shop2007/Amperometro_con_soglia/dc-dc-24-5.jpg

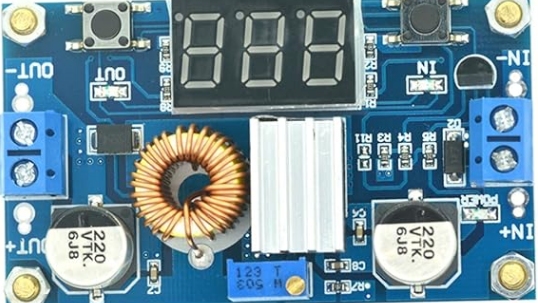
dc-dc-24-5.jpg
