shop2007/Amperometro_con_soglia/doc/pic/Cablaggio.jpg

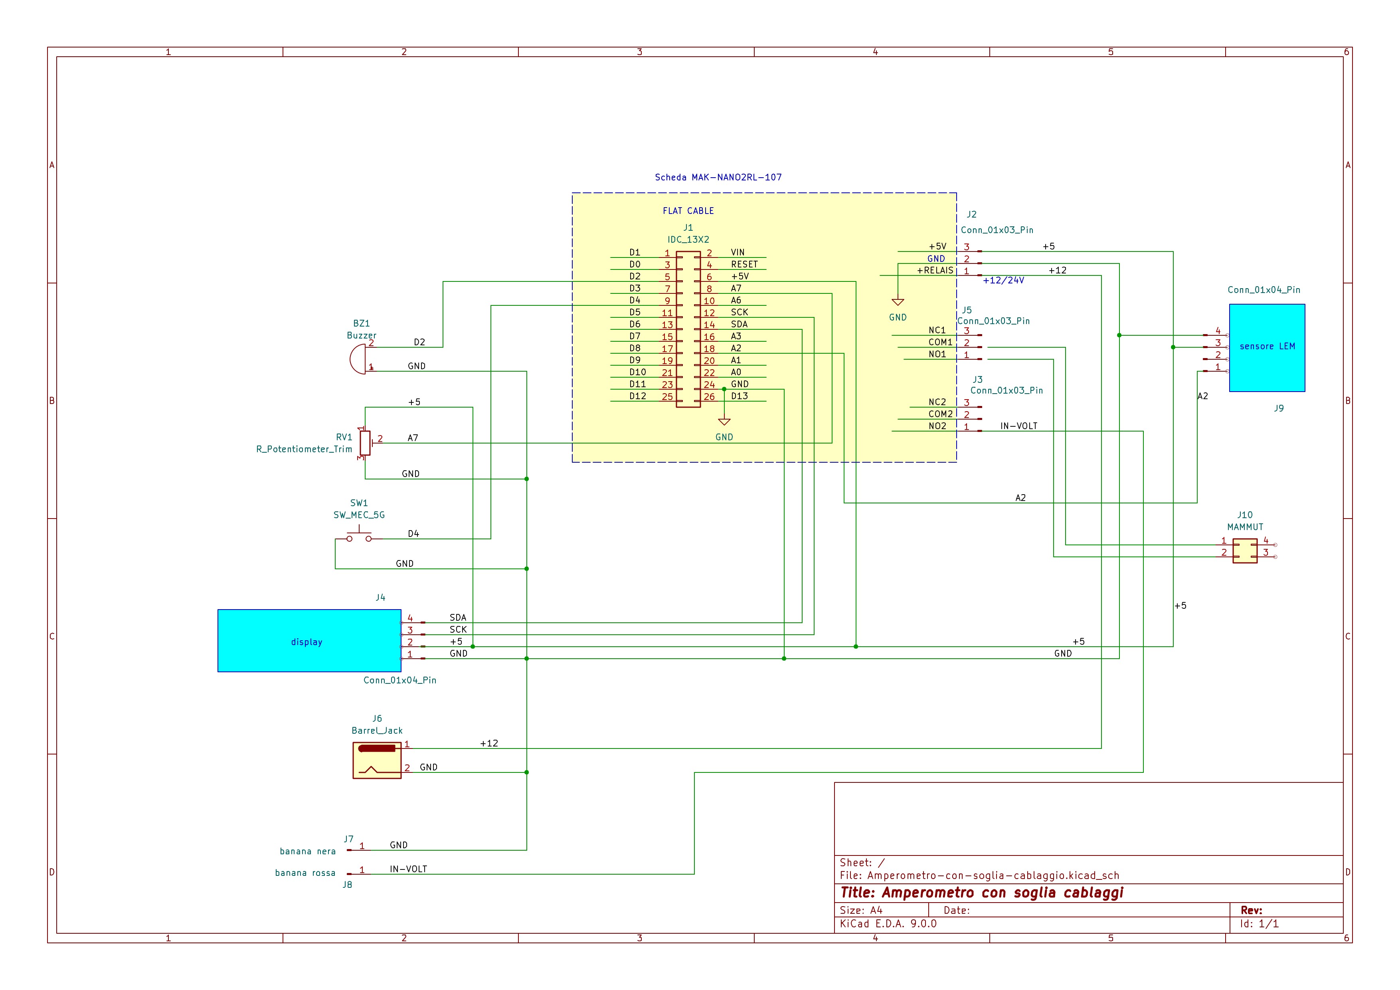
doc/pic/Cablaggio.jpg
