shop2007/Amperometro_con_soglia/doc/pic/Immagine 1.jpg

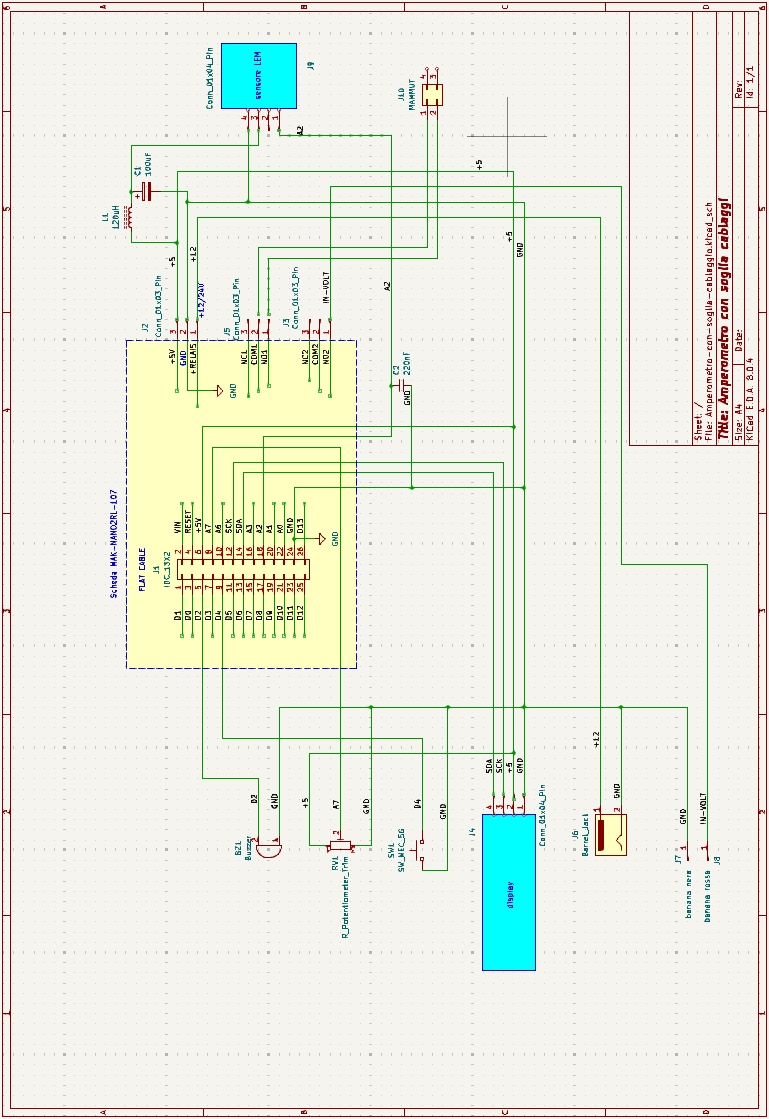
doc/pic/Immagine 1.jpg
