shop2007/Amperometro_con_soglia/doc/pic/Stampa schema - Amperomentro schema vers. SMS.jpg

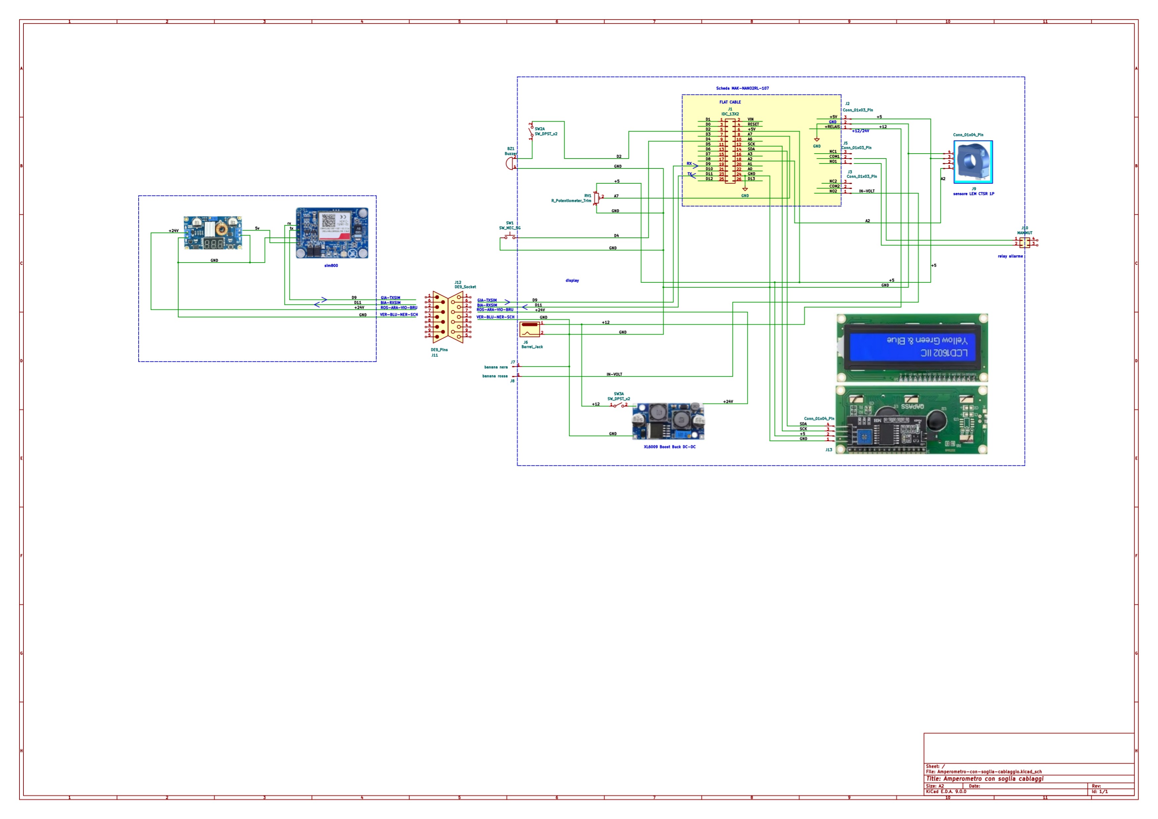
doc/pic/Stampa schema - Amperomentro schema vers. SMS.jpg
