shop2007/Amperometro_con_soglia/kicad/img/LCD1602 I2CAdattatore IIC.png

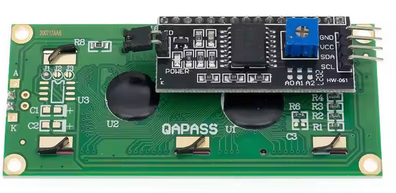
kicad/img/LCD1602 I2CAdattatore IIC.png
