shop2007/Amperometro_con_soglia/kicad/img/lem.jpg

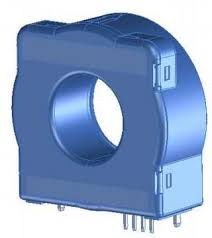
kicad/img/lem.jpg
