shop2007/Amperometro_con_soglia/proto2.jpg

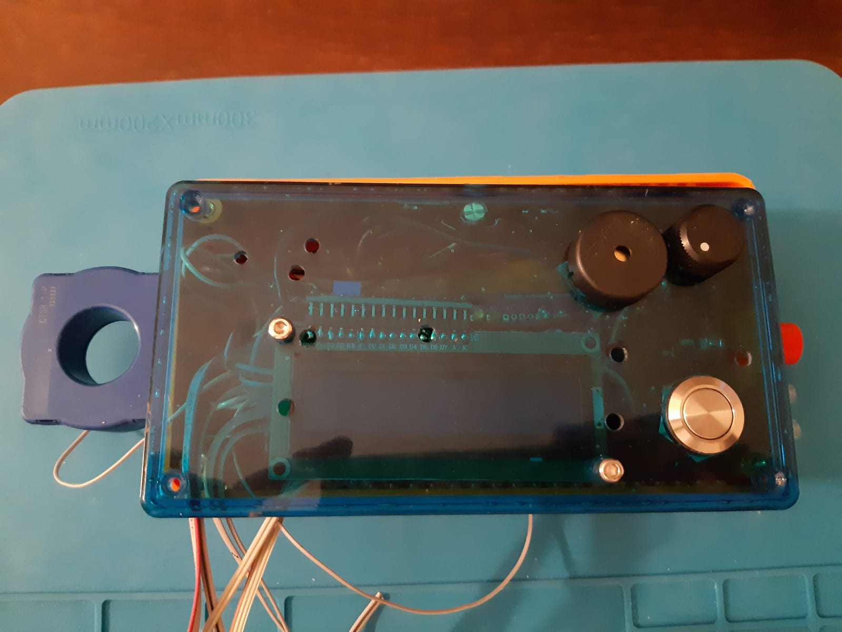
proto2.jpg
