shop2007/Amperometro_con_soglia/proto3.jpg

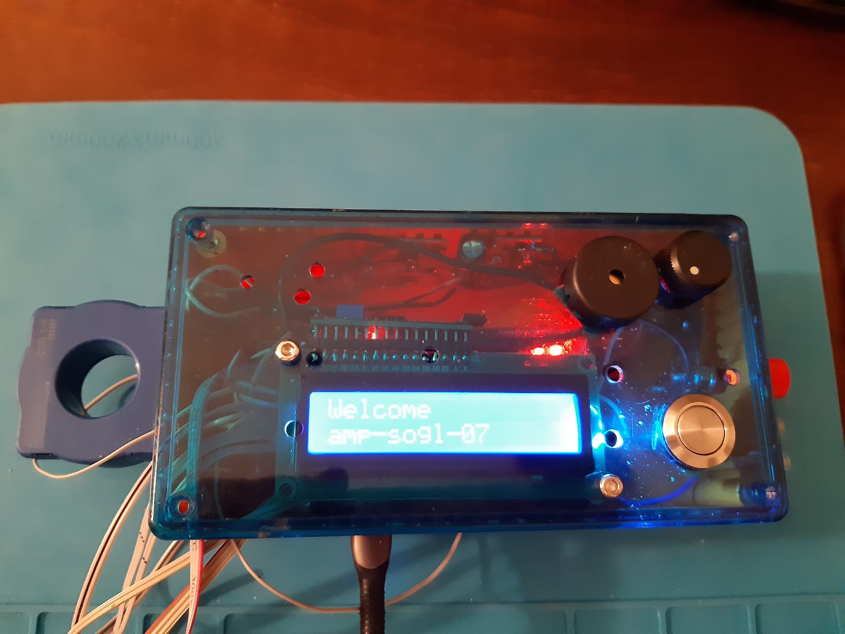
proto3.jpg
