shop2007/Amperometro_con_soglia/proto4.jpg

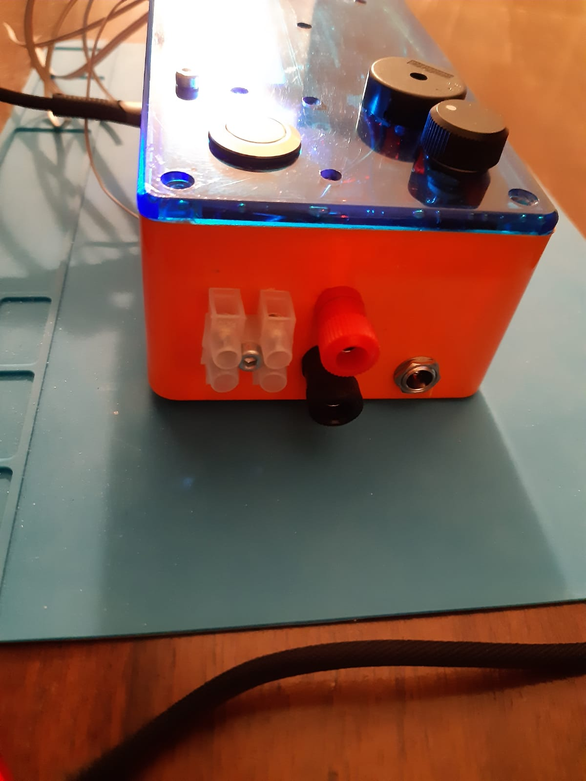
proto4.jpg
