shop2007/Amperometro_con_soglia/proto.jpg

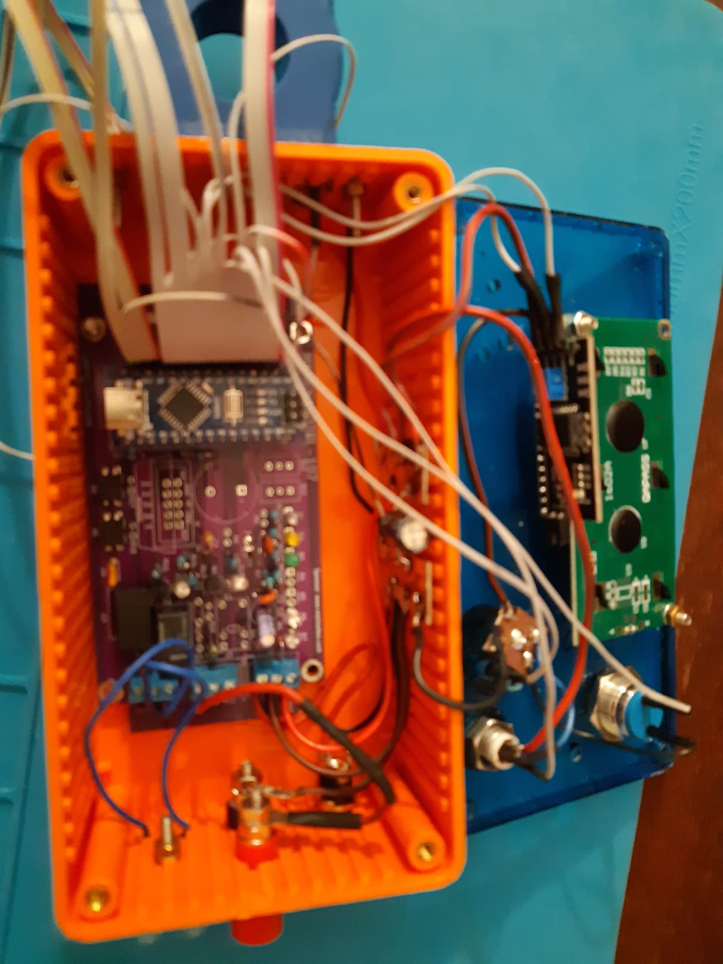
proto.jpg
