shop2007/Amperometro_con_soglia/sim800/Acquisizioni Oscilloscopio/140 connesso verde I_SIM 0.5a-div viola V_SIM 2v-div vswin18v.BMP

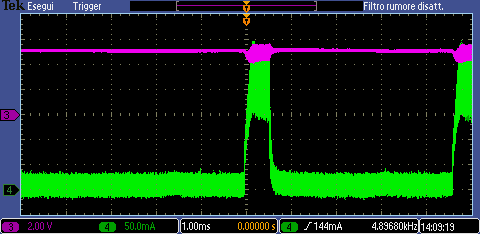
sim800/Acquisizioni Oscilloscopio/140 connesso verde I_SIM 0.5a-div viola V_SIM 2v-div vswin18v.BMP
