shop2007/Amperometro_con_soglia/sim800/Acquisizioni Oscilloscopio/149 fallimento verde I_SIM 1a-div viola V_SIM 2v-div vswin12v.BMP

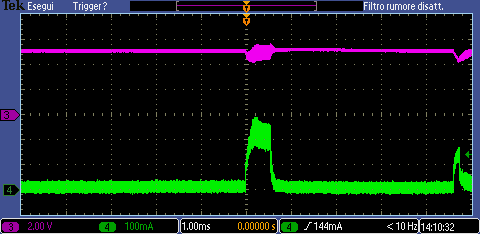
sim800/Acquisizioni Oscilloscopio/149 fallimento verde I_SIM 1a-div viola V_SIM 2v-div vswin12v.BMP
