shop2007/Amperometro_con_soglia/sim800/Acquisizioni Oscilloscopio/TEK00141.BMP

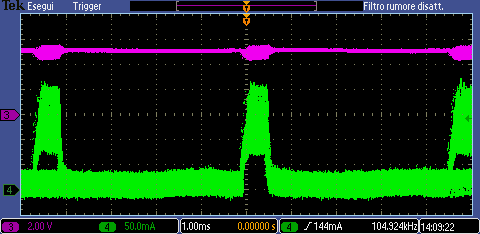
sim800/Acquisizioni Oscilloscopio/TEK00141.BMP
