shop2007/Amperometro_con_soglia/sim800/Acquisizioni Oscilloscopio/TEK00143.BMP

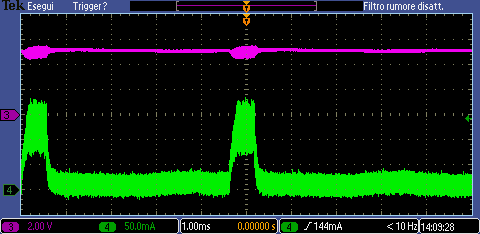
sim800/Acquisizioni Oscilloscopio/TEK00143.BMP
