shop2007/Amperometro_con_soglia/sim800/SCHEMA .png

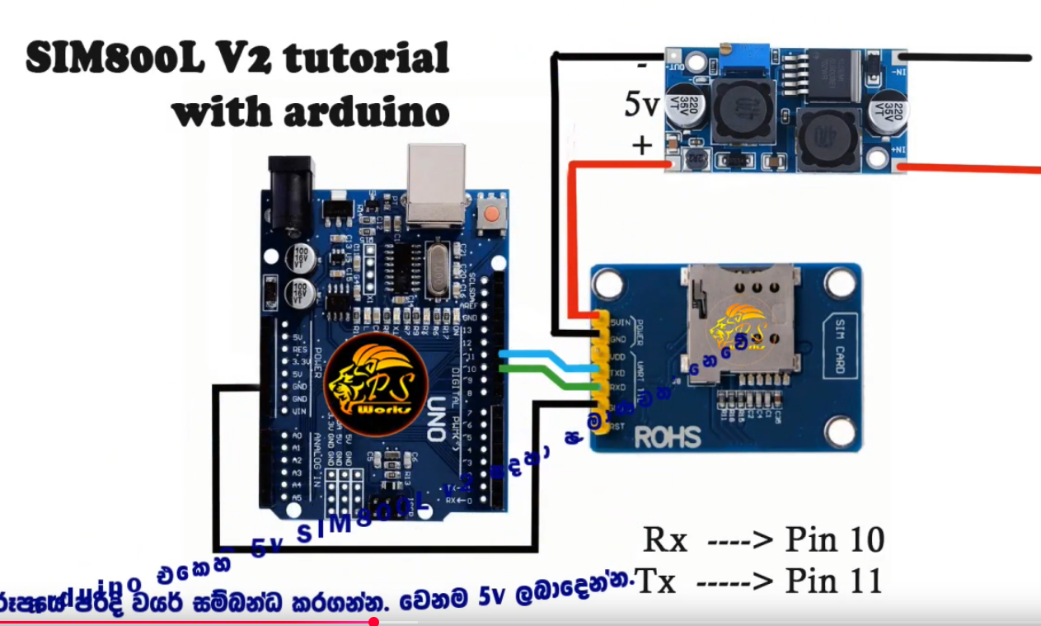
sim800/SCHEMA .png
