shop2007/Amperometro_con_soglia/sim800/YOUTUBE/SIM800L.jpg

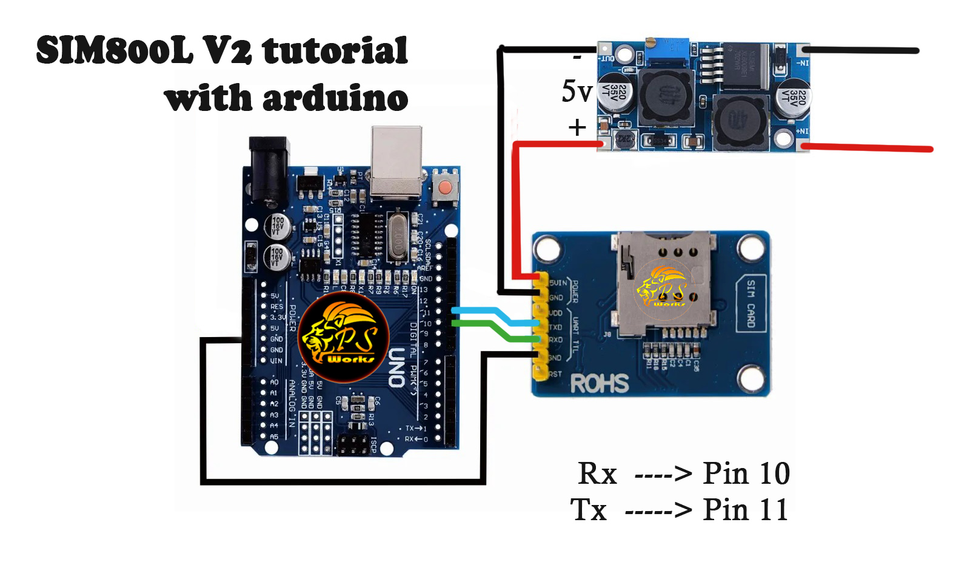
sim800/YOUTUBE/SIM800L.jpg
