shop2007/Amperometro_con_soglia/sim800/YOUTUBE/thumbl.jpg

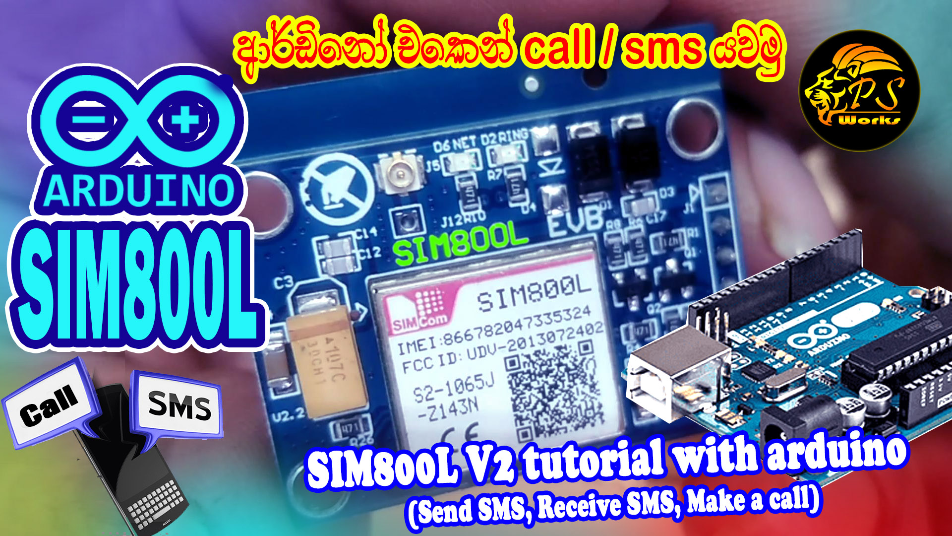
sim800/YOUTUBE/thumbl.jpg
