shop2007/Amperometro_con_soglia/doc/Amperomentro schema vers. SMS.pdf

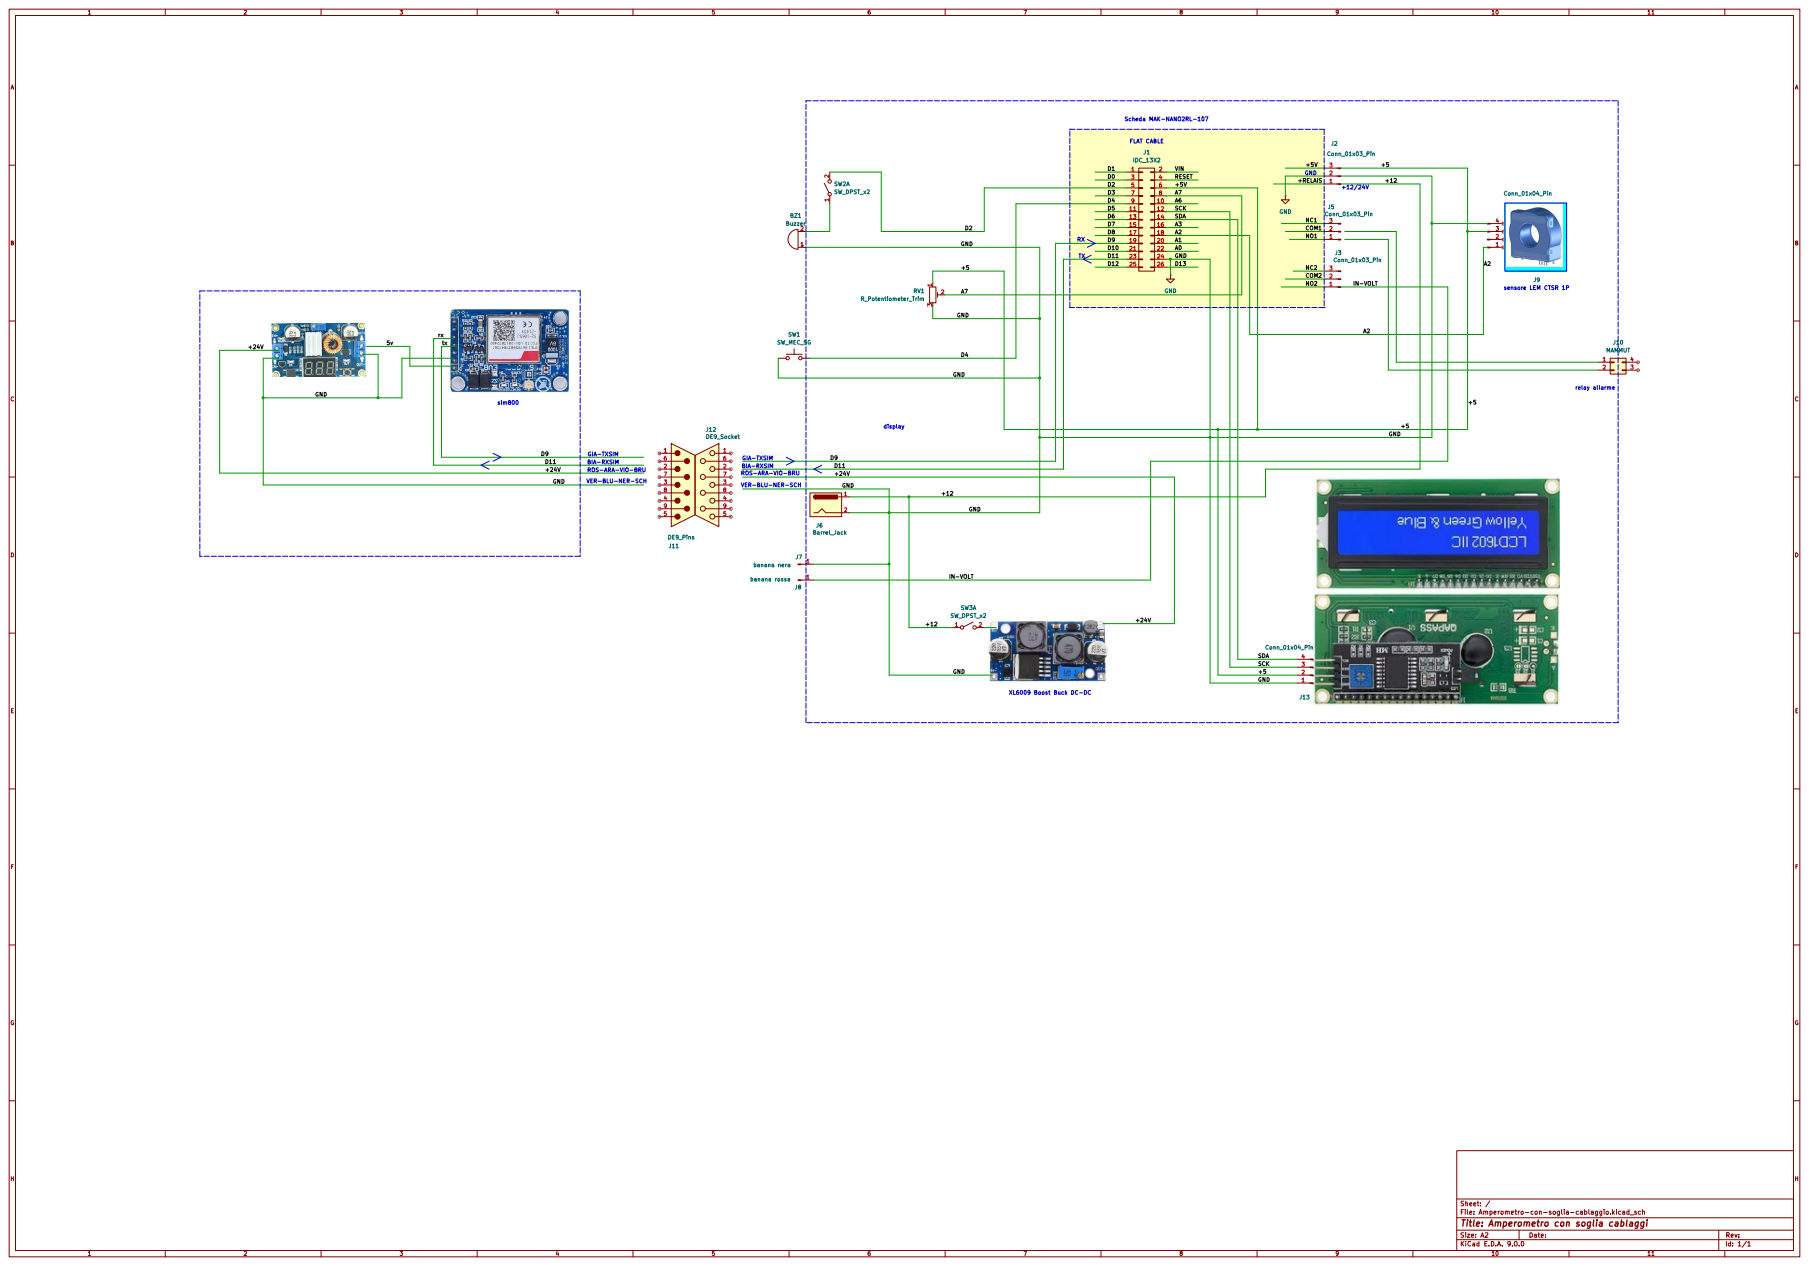
[picture p66: page 1]
