shop2007/Amperometro_con_soglia/kicad/Amperometro-con-soglia-cablaggio.kicad_sch

## KiCad design kicad/Amperometro-con-soglia-cablaggio.kicad_sch (2025-05-17)

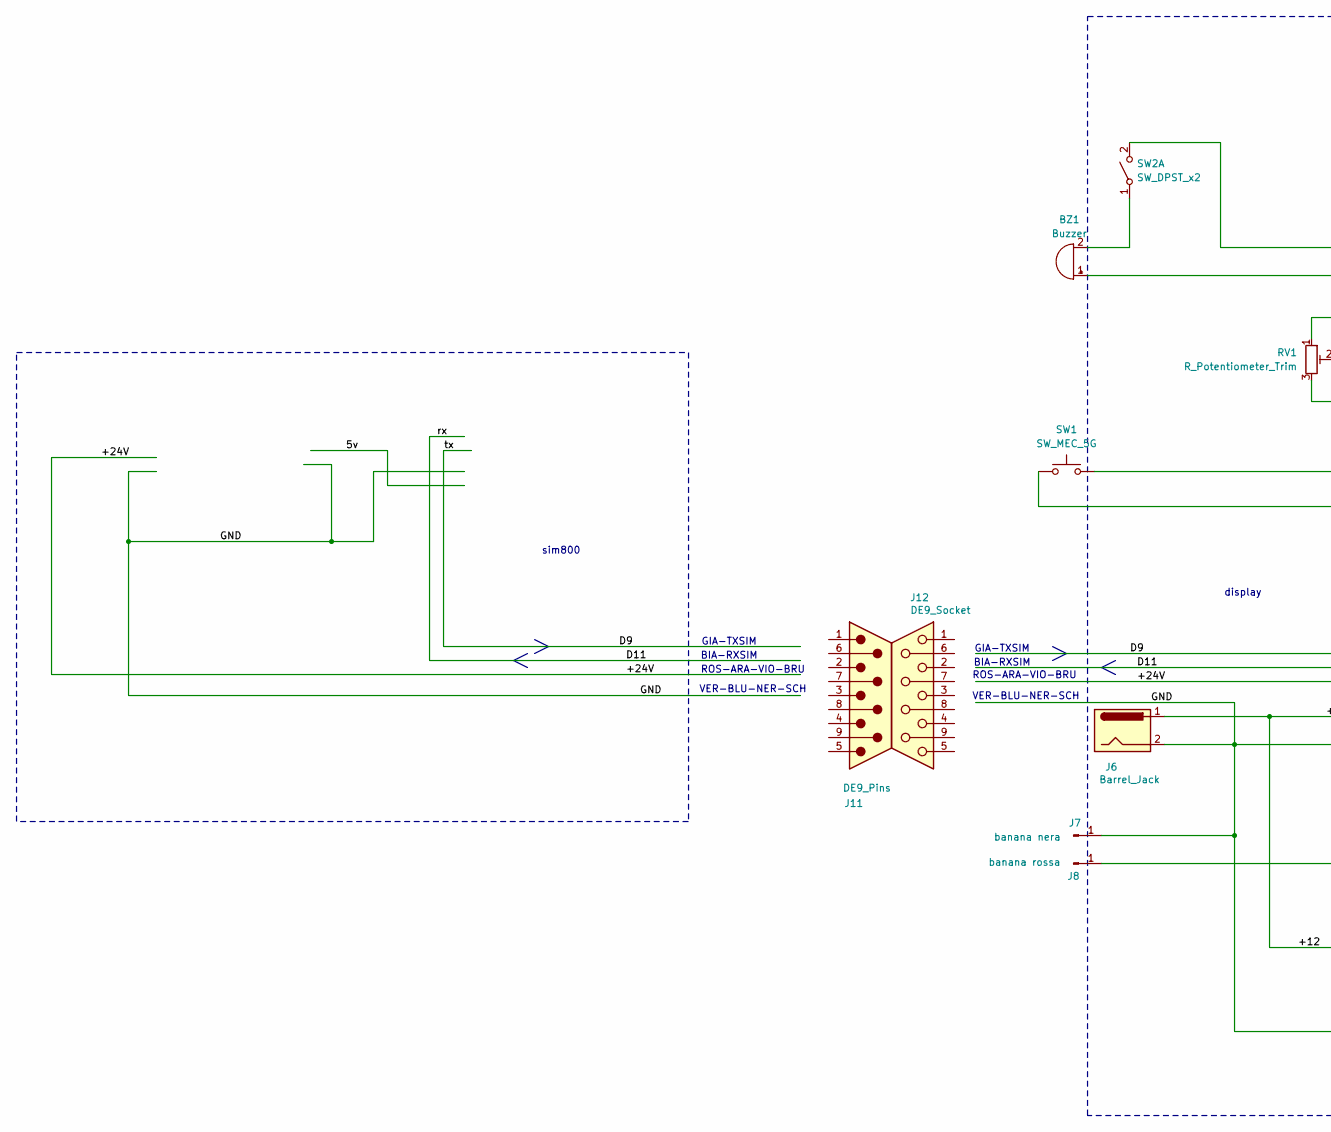
[picture p67: schematic Amperometro-con-soglia-cablaggio.kicad_sch, part in row 1, column 1]

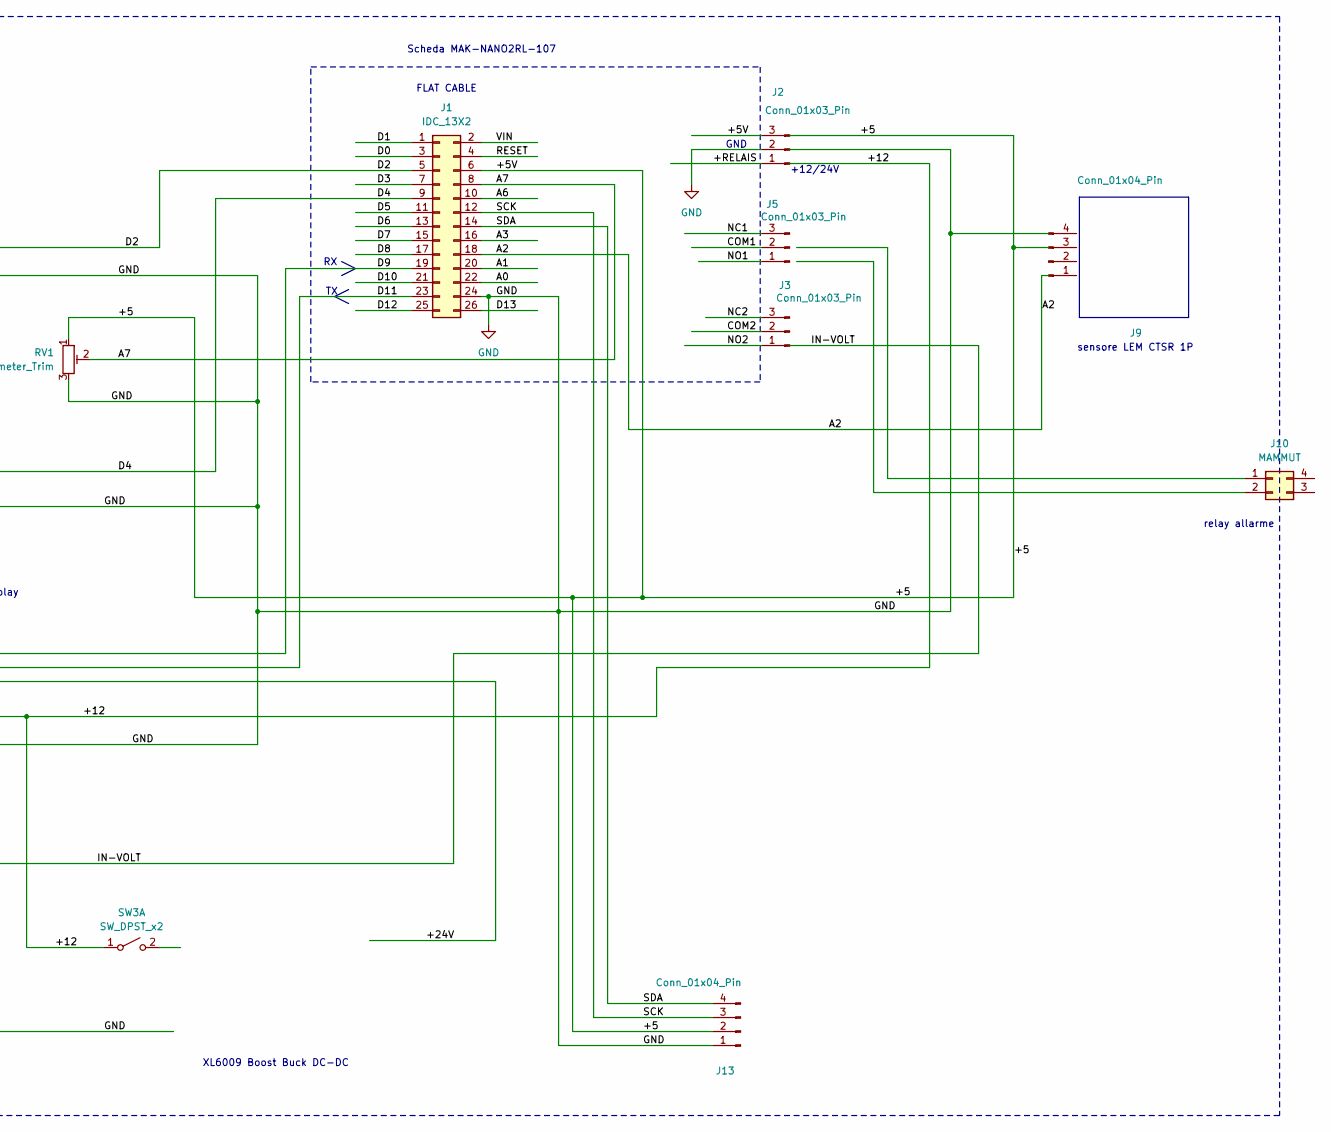
[picture p68: schematic Amperometro-con-soglia-cablaggio.kicad_sch, part in row 1, column 2]

Parts:
BZ1: Buzzer
J1: IDC_13X2; IDC-Header_2x13_P2.54mm_Vertical
J2, J3, J5: Conn_01x03_Pin; Wago_734-133_1x03_P3.50mm_Vertical
J6: Barrel_Jack
J7: banana nera
J8: banana rossa
J9, J13: Conn_01x04_Pin
J10: MAMMUT
J11: DE9_Pins
J12: DE9_Socket
RV1: R_Potentiometer_Trim
SW1: SW_MEC_5G
SW2, SW3: SW_DPST_x2

Connections:
+5: J1.6, J2.3, J13.2, RV1.1
+12: J6.1, SW3.1 (A)
+RELAIS: J2.1
A0: J1.22
A1: J1.20
A2: J1.18
A3: J1.16
A6: J1.10
A7: J1.8, RV1.2
COM1: J5.2
COM2: J3.2
D0: J1.3
D1: J1.1
D2: J1.5, SW2.2 (B)
D3: J1.7
D4: J1.9, SW1.3 (B), SW1.4 (B)
D5: J1.11
D6: J1.13
D7: J1.15
D8: J1.17
D9: J1.19
D10: J1.21
D11: J1.23
D12: J1.25
D13: J1.26
GND: BZ1.1 (+), J1.24, J2.2, J6.2, J7.1, J13.1, RV1.3, SW1.1 (A), SW1.2 (A)
IN-VOLT: J8.1
NC1: J5.3
NC2: J3.3
NO1: J5.1
NO2: J3.1
unnamed: BZ1.2 (-), SW2.1 (A)
RESET: J1.4
SCK: J1.12, J13.3
SDA: J1.14, J13.4
VIN: J1.2

Notes on the sheet:
ROS-ARA-VIO-BRU
relay allarme
Scheda MAK-NANO2RL-107
GND
sensore LEM CTSR 1P
VER-BLU-NER-SCH
BIA-RXSIM
display
GIA-TXSIM
XL6009 Boost Buck DC-DC
sim800
FLAT CABLE
+12/24V
