shop2007/Amperometro_con_soglia/kicad/Amperometro-con-soglia.kicad_sch

## KiCad design kicad/Amperometro-con-soglia.kicad_sch (2025-04-25)

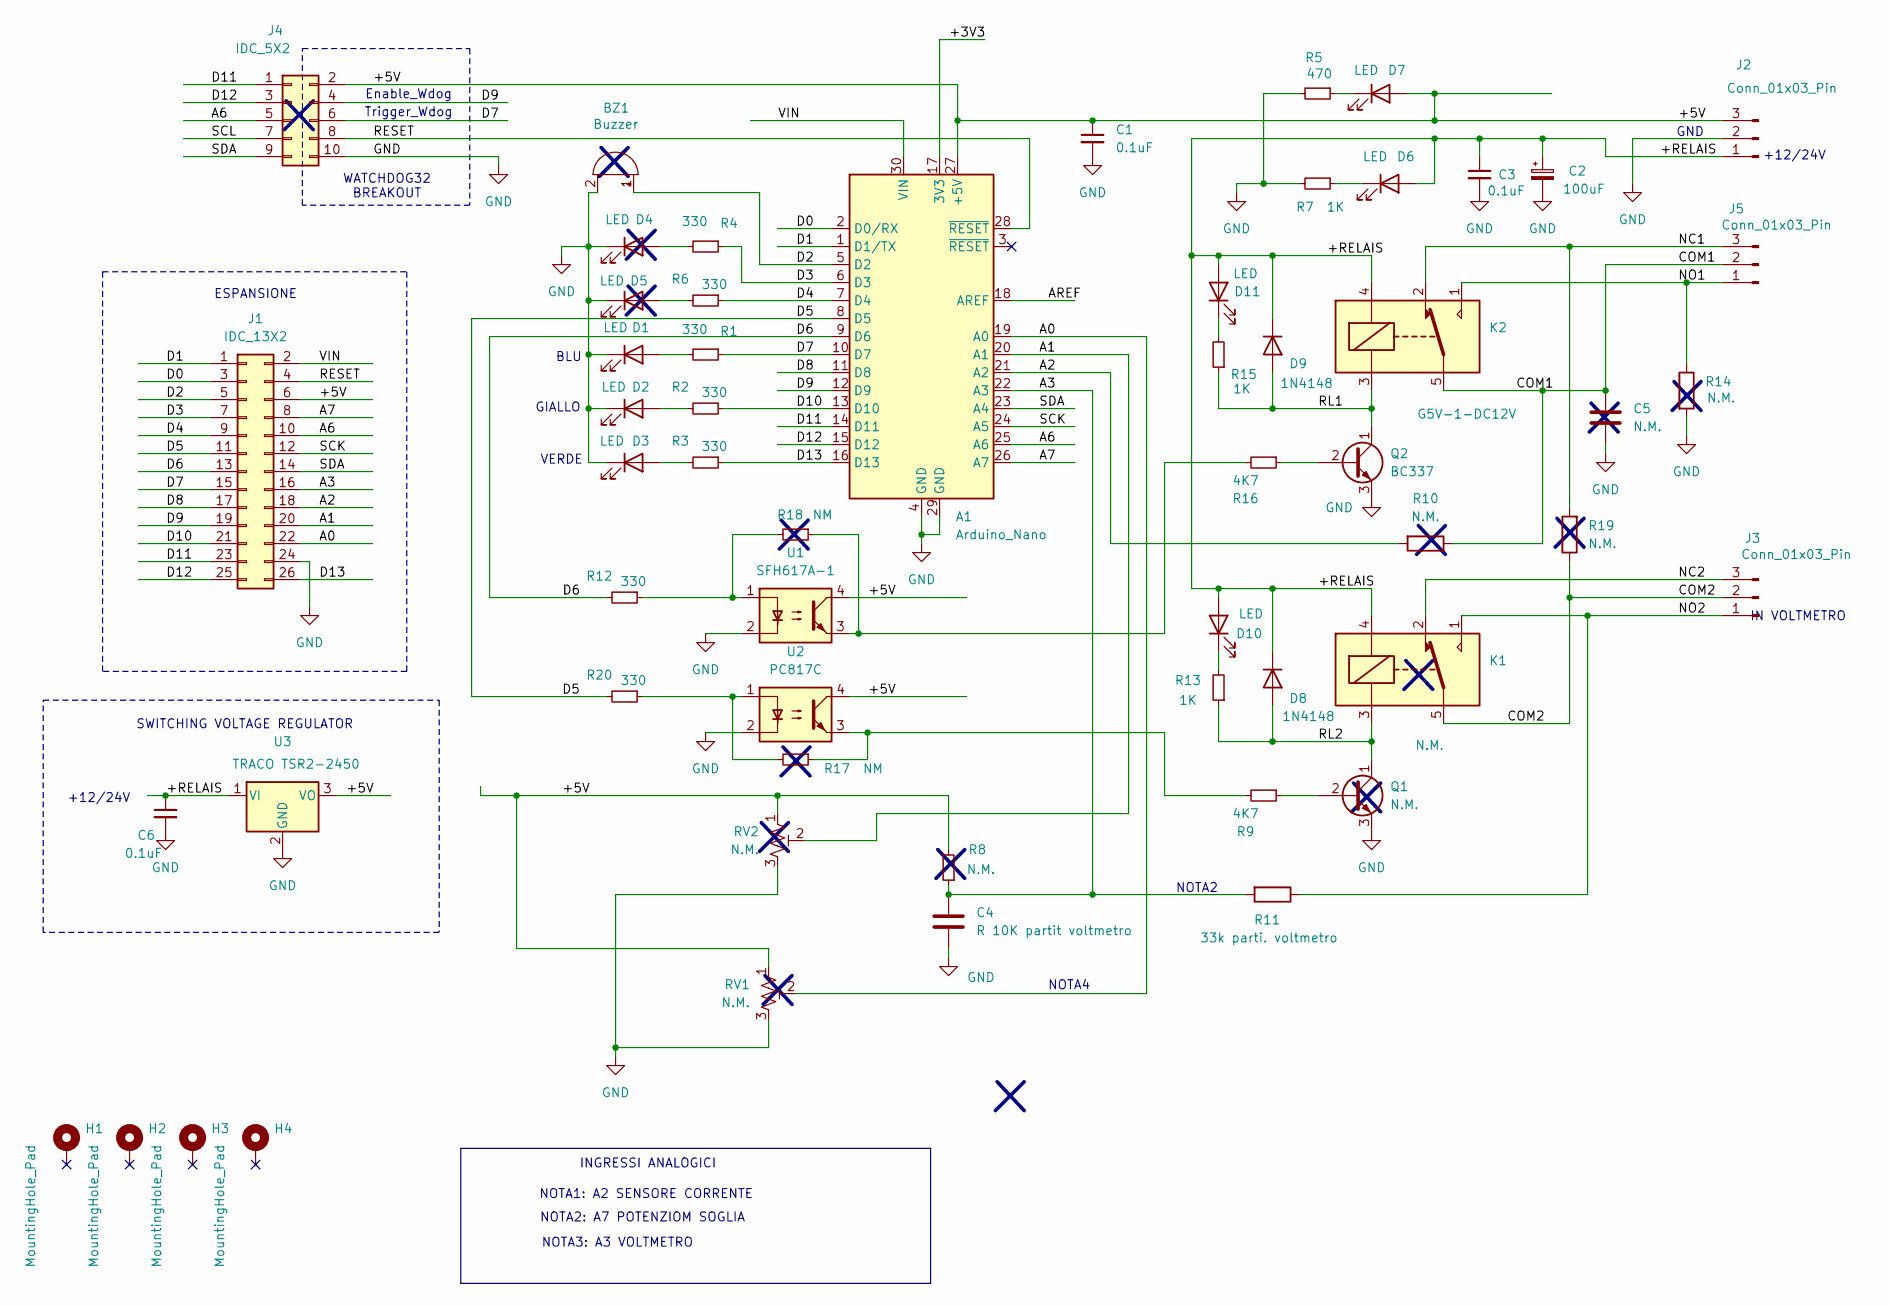
[picture p69: schematic Amperometro-con-soglia.kicad_sch]

Parts:
A1: Arduino_Nano
BZ1: Buzzer; Buzzer_15x7.5RM7.6
C1, C3, C6: 0.1uF; C_Disc_D4.3mm_W1.9mm_P5.00mm
C2: 100uF; C_Radial_D6.3mm_H7.0mm_P2.50mm
C4: R 10K partit voltmetro; C_Disc_D4.3mm_W1.9mm_P5.00mm
C5: N.M.; C_Disc_D4.3mm_W1.9mm_P5.00mm
D1, D2, D3, D4, D5, D6, D7, D10, D11: LED; LED_D3.0mm
D8, D9: 1N4148; D_DO-41_SOD81_P2.54mm_Vertical_AnodeUp
H1, H2, H3, H4: MountingHole_Pad; MountingHole_3.2mm_M3_DIN965_Pad
J1: IDC_13X2; IDC-Header_2x13_P2.54mm_Vertical
J2, J3, J5: Conn_01x03_Pin; Wago_734-133_1x03_P3.50mm_Vertical
J4: IDC_5X2; IDC-Header_2x05_P2.54mm_Vertical
K1: N.M.; Relay_SPDT_HsinDa_Y14
K2: G5V-1-DC12V; Relay_SPDT_HsinDa_Y14
Q1: N.M.; TO-92_HandSolder
Q2: BC337; TO-92_HandSolder
R1, R2, R3, R4, R6, R12, R20: 330; R_Axial_DIN0204_L3.6mm_D1.6mm_P2.54mm_Vertical
R5: 470; R_Axial_DIN0204_L3.6mm_D1.6mm_P2.54mm_Vertical
R7, R13, R15: 1K; R_Axial_DIN0204_L3.6mm_D1.6mm_P2.54mm_Vertical
R8, R10, R14, R19: N.M.; R_Axial_DIN0204_L3.6mm_D1.6mm_P2.54mm_Vertical
R9, R16: 4K7; R_Axial_DIN0204_L3.6mm_D1.6mm_P2.54mm_Vertical
R11: 33k parti. voltmetro; R_Axial_DIN0204_L3.6mm_D1.6mm_P2.54mm_Vertical
R17, R18: NM; R_Axial_DIN0204_L3.6mm_D1.6mm_P2.54mm_Vertical
RV1, RV2: N.M.; Potentiometer_Bourns_3296W_Vertical
U1: SFH617A-1; DIP-4_W7.62mm
U2: PC817C; DIP-4_W7.62mm
U3: TRACO TSR2-2450; Converter_DCDC_TRACO_TSR-1_THT

Connections:
+3V3: A1.17 (3V3)
+5V: A1.27 (+5V), C1.1, D7.2 (A), J1.6, J2.3, J4.2, R8.2, RV1.1, RV2.1, U1.4, U2.4, U3.3 (VO)
+RELAIS: C2.1, C3.1, C6.1, D6.2 (A), D8.1 (K), D9.1 (K), D10.2 (A), D11.2 (A), J2.1, K1.4, K2.4, U3.1 (VI)
A0: A1.19 (A0), J1.22, RV1.2
A1: A1.20 (A1), J1.20, RV2.2
A2: A1.21 (A2), J1.18, R10.2
A3: A1.22 (A3), C4.1, J1.16, R8.1, R11.2
A6: A1.25 (A6), J1.10, J4.5
A7: A1.26 (A7), J1.8
AREF: A1.18 (AREF)
COM1: C5.1, J5.2, K2.5, K2.6, R10.1
COM2: J3.2, K1.5, K1.6, R19.1
D0: A1.2 (D0/RX), J1.3
D1: A1.1 (D1/TX), J1.1
D2: A1.5 (D2), BZ1.1 (+), J1.5
D3: A1.6 (D3), J1.7, R4.1
D4: A1.7 (D4), J1.9, R6.1
D5: A1.8 (D5), J1.11, R20.2
D6: A1.9 (D6), J1.13, R12.2
D7: A1.10 (D7), J1.15, J4.6, R1.1
D8: A1.11 (D8), J1.17
D9: A1.12 (D9), J1.19, J4.4
D10: A1.13 (D10), J1.21, R2.1
D11: A1.14 (D11), J1.23, J4.1
D12: A1.15 (D12), J1.25, J4.3
D13: A1.16 (D13), J1.26, R3.1
GND: A1.4 (GND), A1.29 (GND), BZ1.2 (-), C1.2, C2.2, C3.2, C4.2, C5.2, C6.2, D1.1 (K), D2.1 (K), D3.1 (K), D4.1 (K), D5.1 (K), J1.24, J2.2, J4.10, Q1.3 (E), Q2.3 (E), R5.2, R7.2, R14.2, RV1.3, RV2.3, U1.2, U2.2, U3.2 (GND)
NC1: J5.3, K2.2, R19.2
NC2: J3.3, K1.2
NO1: J5.1, K2.1, R14.1
NO2: J3.1, K1.1, R11.1
unnamed: D1.2 (A), R1.2
unnamed: D2.2 (A), R2.2
unnamed: D3.2 (A), R3.2
unnamed: D4.2 (A), R4.2
unnamed: D5.2 (A), R6.2
unnamed: D6.1 (K), R7.1
unnamed: D7.1 (K), R5.1
unnamed: D10.1 (K), R13.2
unnamed: D11.1 (K), R15.2
unnamed: Q1.2 (B), R9.1
unnamed: Q2.2 (B), R16.1
unnamed: R12.1, R18.2, U1.1
unnamed: R16.2, R18.1, U1.3
unnamed: R9.2, R17.1, U2.3
unnamed: R17.2, R20.1, U2.1
RESET: A1.28 (~RESET), J1.4, J4.8
RL1: D9.2 (A), K2.3, Q2.1 (C), R15.1
RL2: D8.2 (A), K1.3, Q1.1 (C), R13.1
SCK: A1.24 (A5), J1.12
SCL: J4.7
SDA: A1.23 (A4), J1.14, J4.9
VIN: A1.30 (VIN), J1.2

Notes on the sheet:
VERDE
NOTA1: A2 SENSORE CORRENTE
WATCHDOG32 BREAKOUT
GND
INGRESSI ANALOGICI
GIALLO
NOTA3: A3 VOLTMETRO
+12/24V
SWITCHING VOLTAGE REGULATOR
NOTA2: A7 POTENZIOM SOGLIA
BLU
ESPANSIONE
IN VOLTMETRO
NOTA4
Enable_Wdog
NOTA2
Trigger_Wdog
